solvek/AirOk/Images/ESP8266.jpg

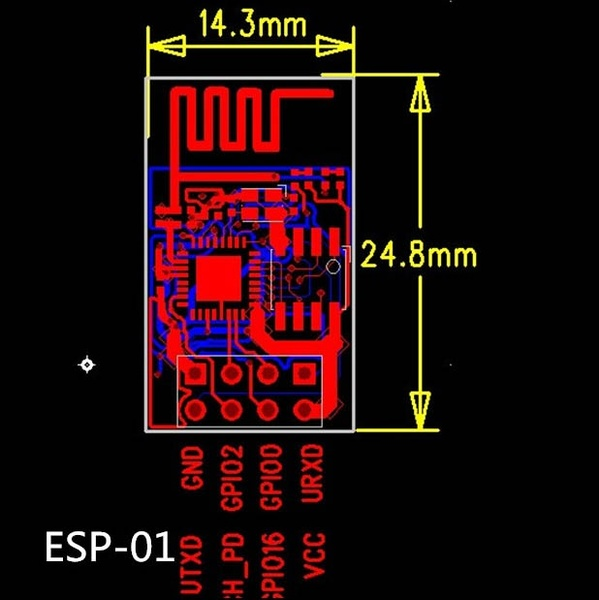
Images/ESP8266.jpg
