solvek/AirOk/Images/Voltage.jpg

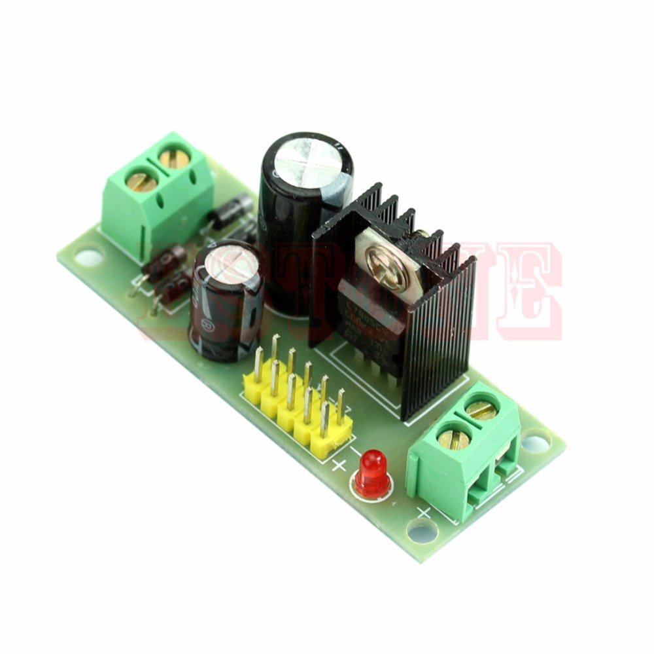
Images/Voltage.jpg
